TheTosters/HeaterControl/include/rgb_led.h

/*
MIT License

Copyright (c) 2018 Bartłomiej Żarnowski

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
rgb_led.h
Created on: Oct 7, 2019
    Author: Bartłomiej Żarnowski (Toster)
*/
#ifndef rgb_led_hpp
#define rgb_led_hpp

extern "C" {
#include <components/boards/boards.h>
}
#include <stdint.h>
#include "types/hardware_pin.h"
#include "timer_owner.h"

class RGBLed : TimerOwner {
public:
    enum class Color {
      NONE, RED, GREEN, BLUE, YELLOW, WHITE, CYAN
    };

    RGBLed(HardwarePin r, HardwarePin g, HardwarePin b) :
      TimerOwner(false, RGBLed::timerHandler),
      rPin(r), gPin(g), bPin(b)
    {
      pinUp(rPin);
      pinUp(gPin);
      pinUp(bPin);
    }

    void setColor(const Color& col, const unsigned int timeoutMs) {
      setColor(col);
      startTimer(timeoutMs);
    }

    void setColor(const Color& col) {
      stopTimer();
      pinUp(rPin);
      pinUp(gPin);
      pinUp(bPin);
      switch(col) {
        case Color::RED:
          pinDown(rPin);
          break;
        case Color::GREEN:
          pinDown(gPin);
          break;
        case Color::BLUE:
          pinDown(bPin);
          break;
        case Color::YELLOW:
          pinDown(rPin);
          pinDown(gPin);
          break;
        case Color::CYAN:
          pinDown(bPin);
          pinDown(gPin);
          break;
        case Color::WHITE:
          pinDown(rPin);
          pinDown(gPin);
          pinDown(bPin);
          break;
        default:
        case Color::NONE:
          break;
      }
    }
private:
    HardwarePin rPin;
    HardwarePin gPin;
    HardwarePin bPin;

    static void timerHandler(void* selfPtr) {
      static_cast<RGBLed*>(selfPtr)->setColor(Color::NONE);
    }

    void pinUp(const HardwarePin& pin) {
      nrf_gpio_cfg(
                    pin.get(),
                    NRF_GPIO_PIN_DIR_OUTPUT,
                    NRF_GPIO_PIN_INPUT_DISCONNECT,
                    NRF_GPIO_PIN_PULLUP,
                    NRF_GPIO_PIN_S0S1,
                    NRF_GPIO_PIN_NOSENSE);
    }

    void pinDown(const HardwarePin& pin) {
          nrf_gpio_cfg(
                        pin.get(),
                        NRF_GPIO_PIN_DIR_OUTPUT,
                        NRF_GPIO_PIN_INPUT_DISCONNECT,
                        NRF_GPIO_PIN_PULLDOWN,
                        NRF_GPIO_PIN_S0S1,
                        NRF_GPIO_PIN_NOSENSE);
        }
};

RGBLed& RGBLeds();
#endif /* rgb_led_hpp */
