TheTosters/HeaterControl/include/xbm_icons.h

#pragma once

#include "icon_bridge.h"
#include <stdint.h>

const IconBridge flameIcon{ 16, 16, {
  0x00, 0x00, 0x40, 0x00, 0x80, 0x01, 0x80, 0x03, 0xC0, 0x07, 0xE0, 0x0F,
  0xE0, 0x0F, 0xF0, 0x1F, 0x78, 0x1F, 0x78, 0x1E, 0x38, 0x1E, 0x38, 0x1C,
  0x30, 0x0C, 0x20, 0x0C, 0x20, 0x00, 0x00, 0x00 }};
